zhaofengzf163/Eshail2-QO100-Simple-Frequency-Converter/ADF4351-PTT-20190920/arduino-t13.jpg

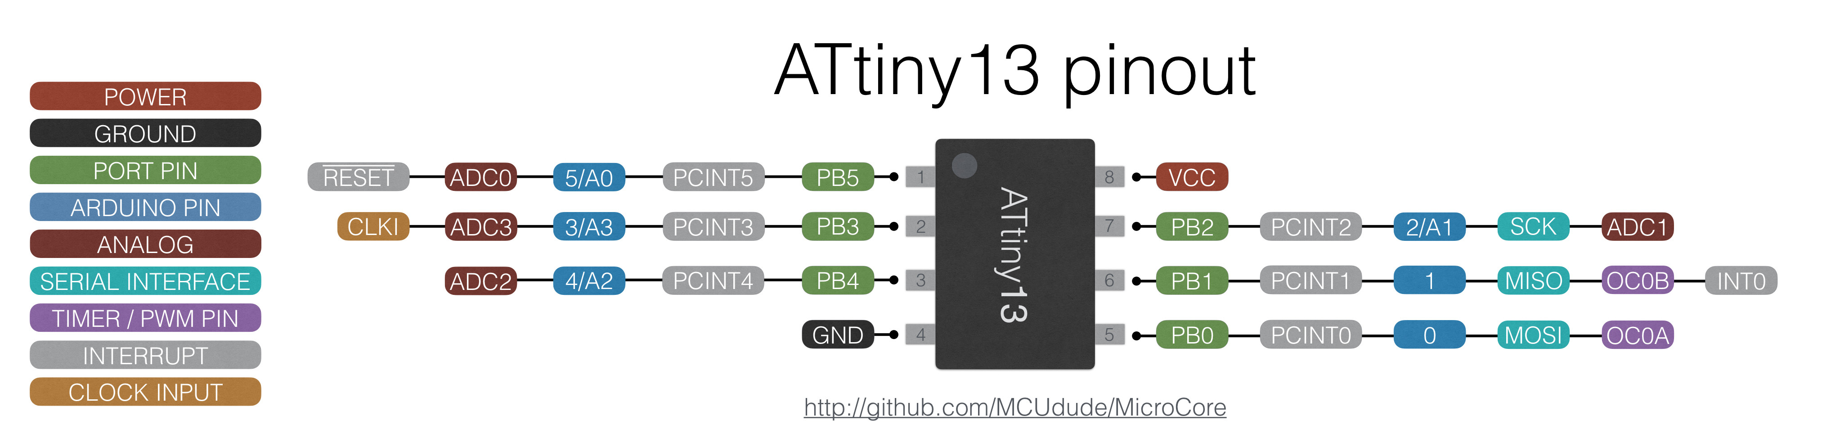
ADF4351-PTT-20190920/arduino-t13.jpg
