zhaofengzf163/Eshail2-QO100-Simple-Frequency-Converter/ADF4351-PTT-20190920/t13-adf4351.png

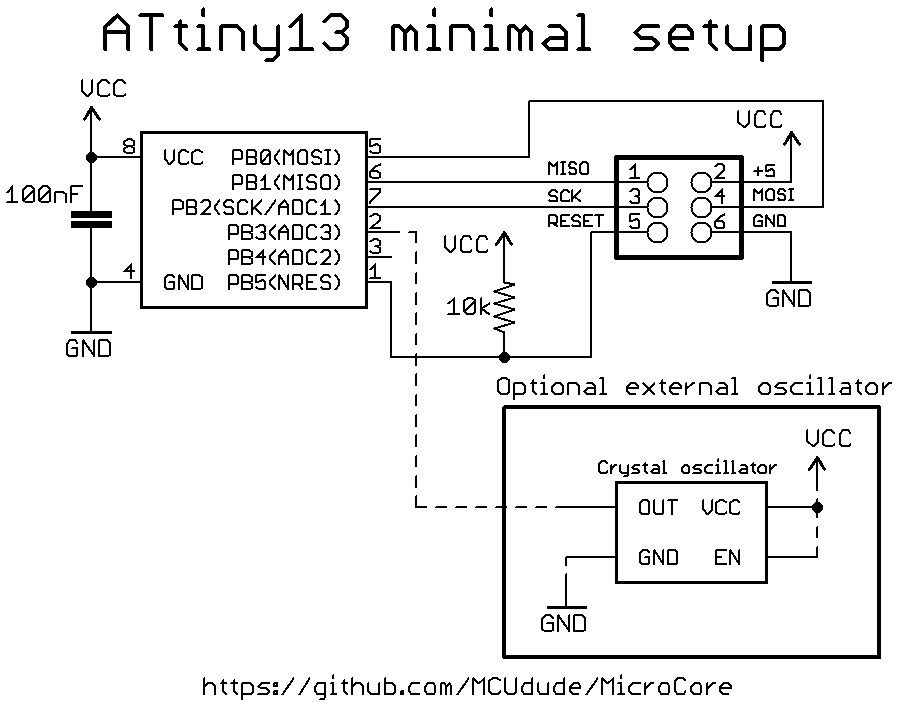
ADF4351-PTT-20190920/t13-adf4351.png
