zhaofengzf163/Eshail2-QO100-Simple-Frequency-Converter/image/1-3.jpg

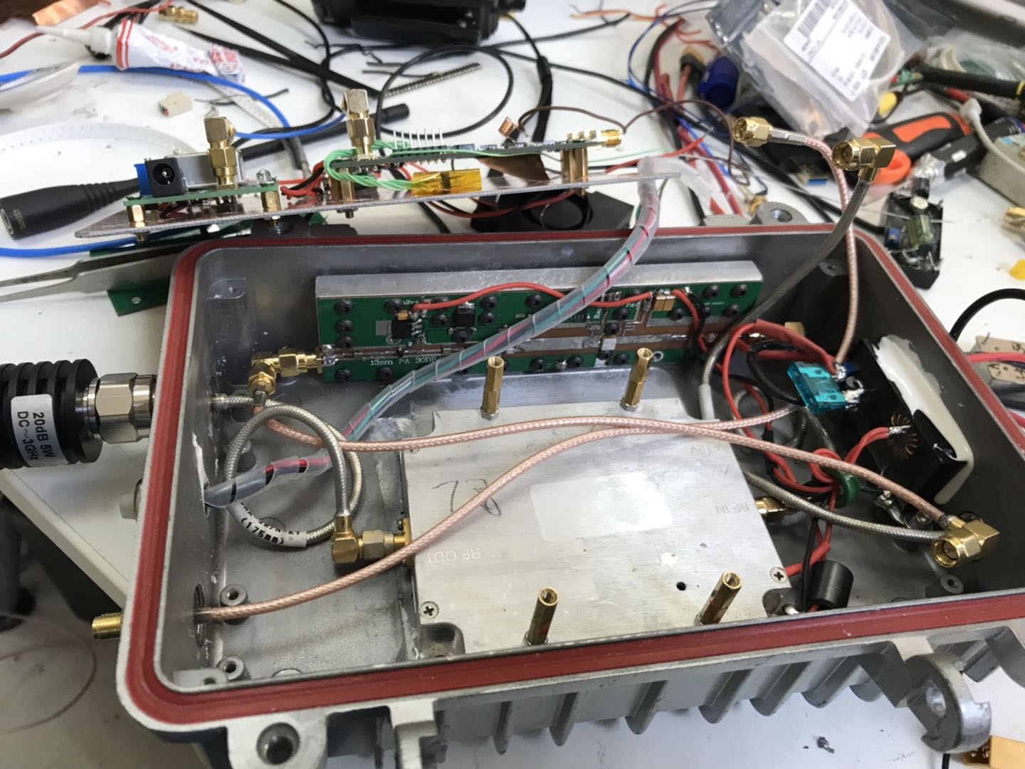
image/1-3.jpg
