zhaofengzf163/Eshail2-QO100-Simple-Frequency-Converter/image/2-2.jpg

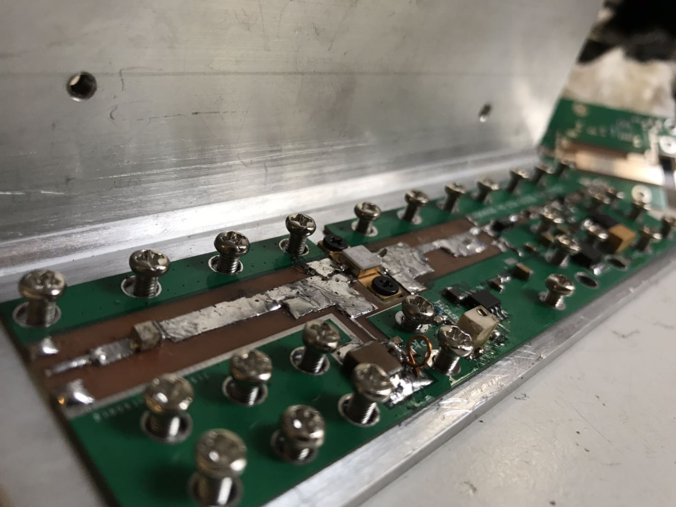
image/2-2.jpg
