zhaofengzf163/Eshail2-QO100-Simple-Frequency-Converter/image/2-3.jpg

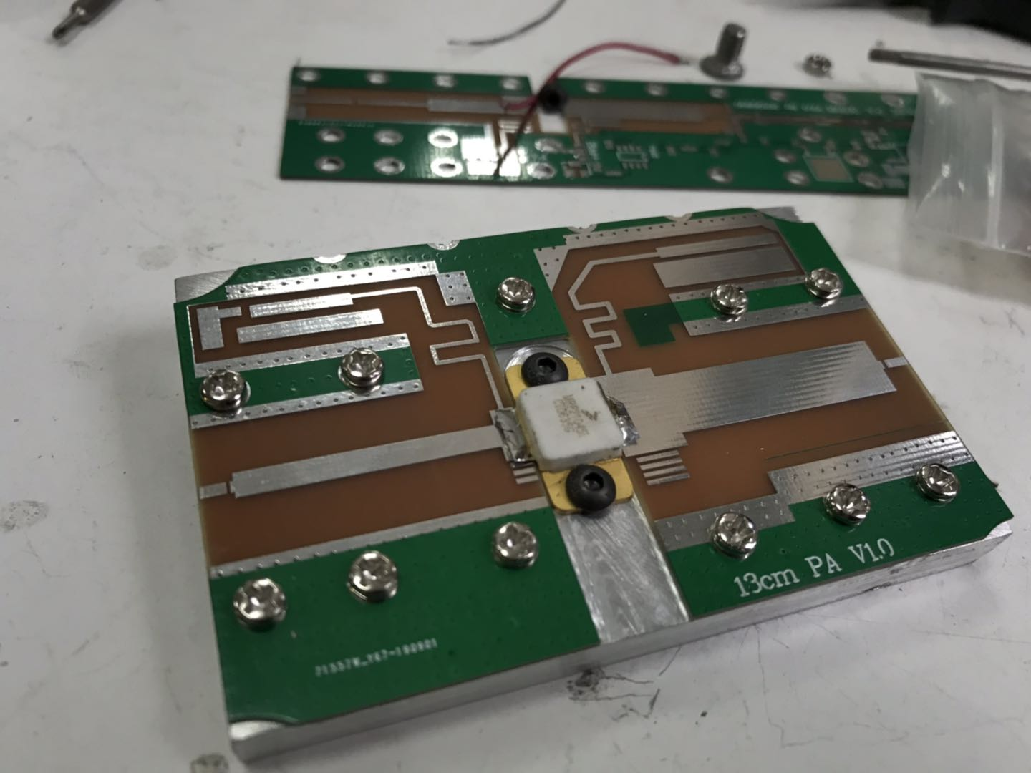
image/2-3.jpg
