zhaofengzf163/Eshail2-QO100-Simple-Frequency-Converter/image/2-4.jpg

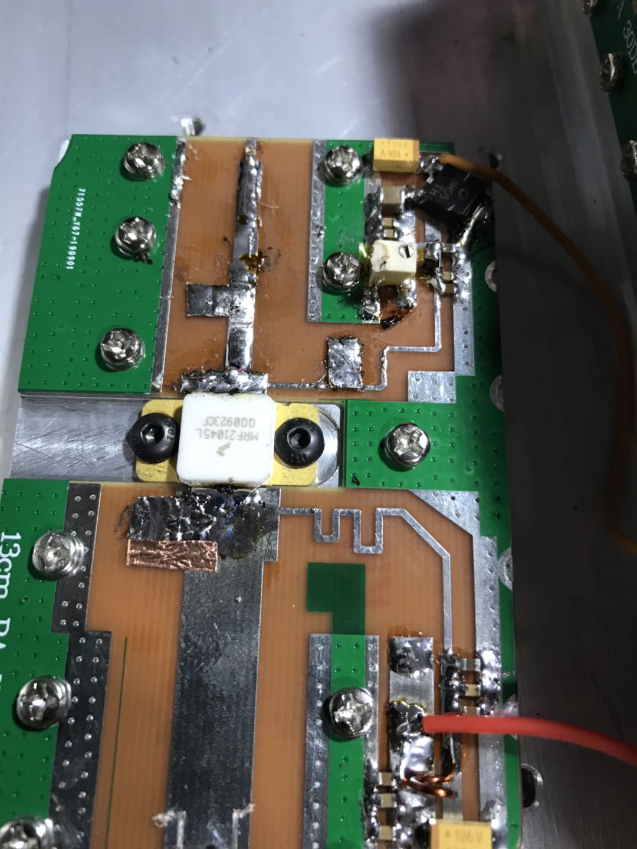
image/2-4.jpg
