zhaofengzf163/Eshail2-QO100-Simple-Frequency-Converter/image/flir-1.jpg

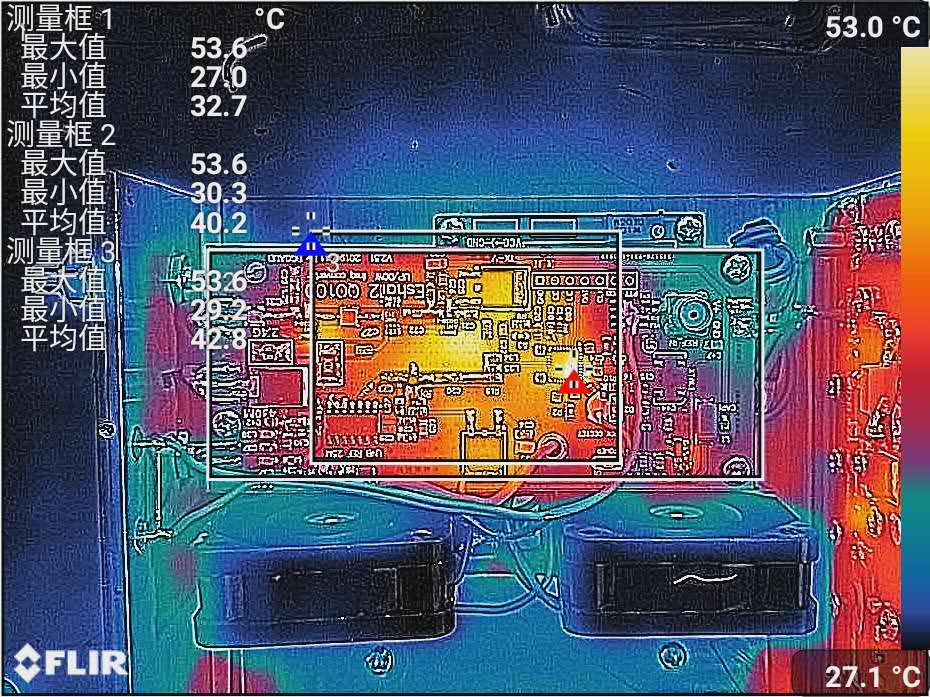
image/flir-1.jpg
