zhaofengzf163/Eshail2-QO100-Simple-Frequency-Converter/image/flir-3.jpg

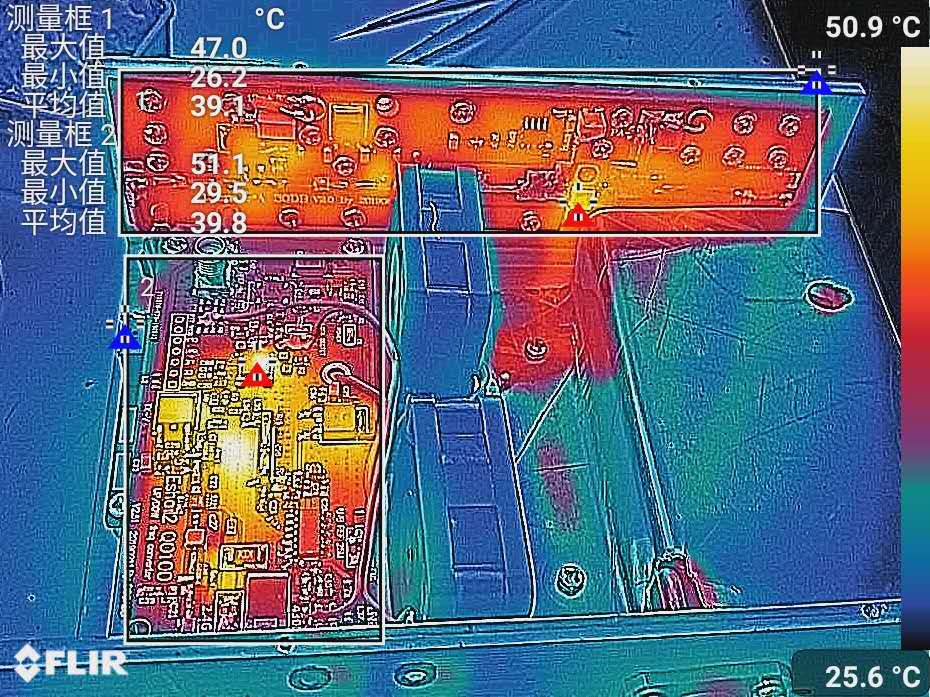
image/flir-3.jpg
