zhaofengzf163/Eshail2-QO100-Simple-Frequency-Converter/说明文档/13CMPA_MRF21045_V1.1.png

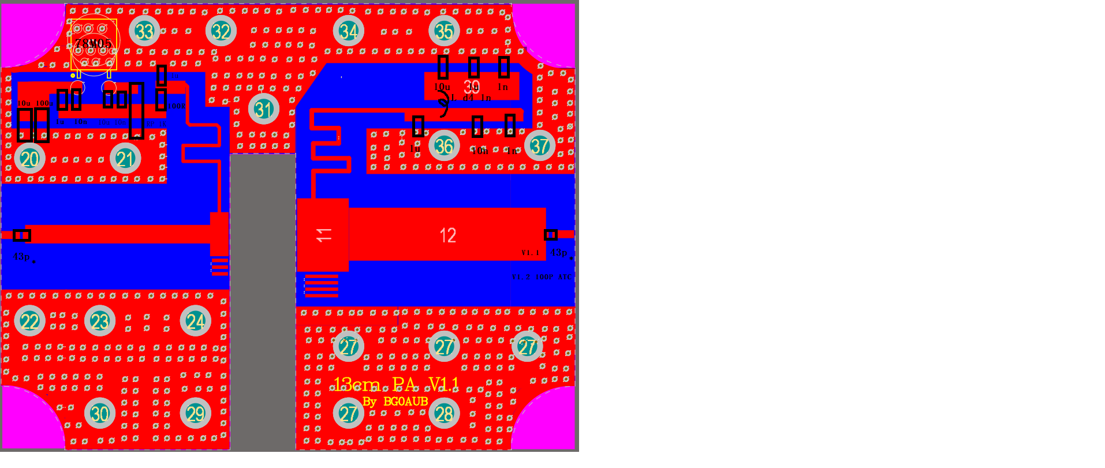
说明文档/13CMPA_MRF21045_V1.1.png
