zhaofengzf163/Eshail2-QO100-Simple-Frequency-Converter/说明文档/auto_PTT.png

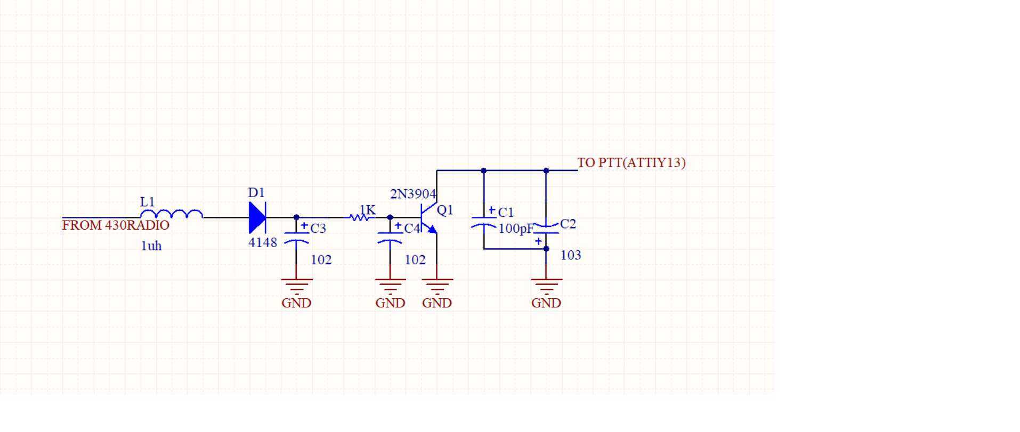
说明文档/auto_PTT.png
