zhaofengzf163/Eshail2-QO100-Simple-Frequency-Converter/说明文档/补充说明.png

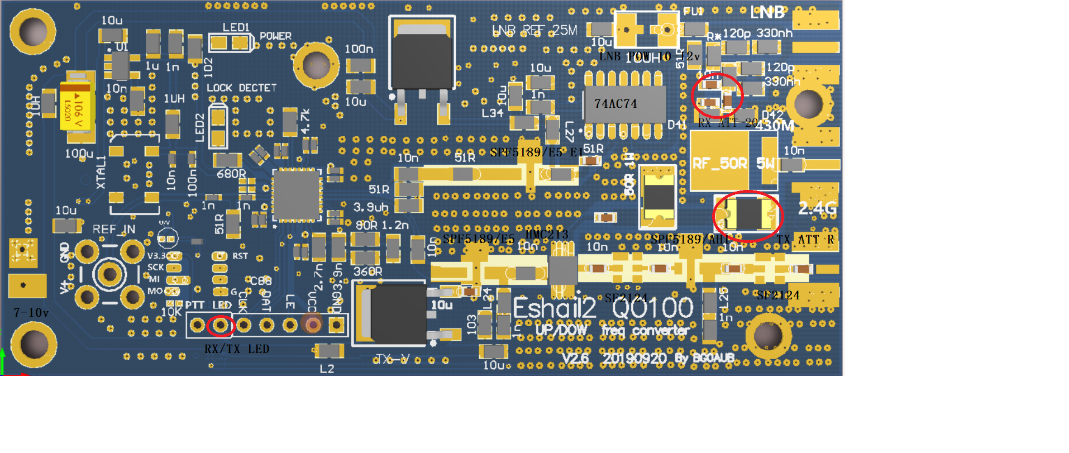
说明文档/补充说明.png
